siro20/P1P2_HBS_USBCdc_Modem/kicad/p1p2_pi_hat.png

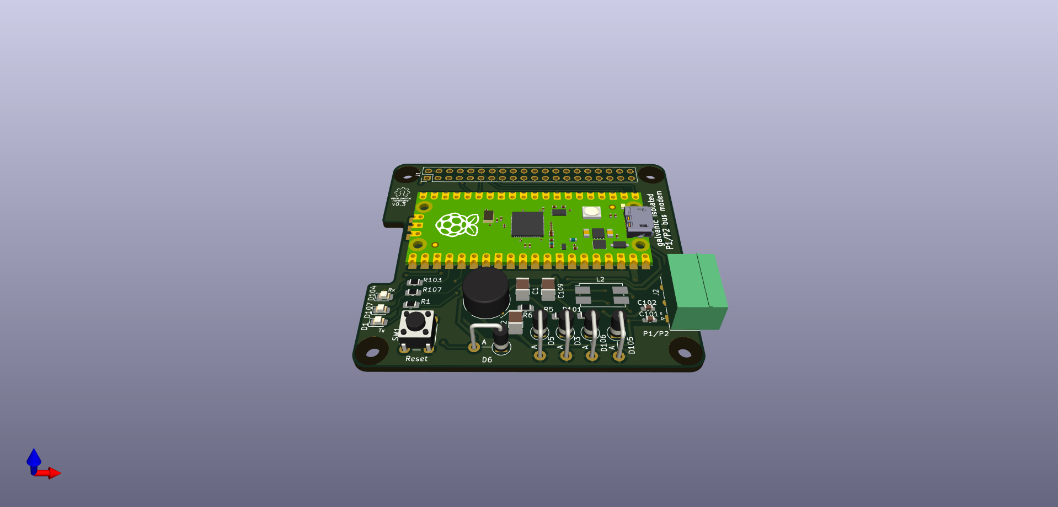
kicad/p1p2_pi_hat.png
