siro20/P1P2_HBS_USBCdc_Modem/pico/src/shiftreg.hpp

#pragma once
#include "inttypes.h"
#include <string.h>
#include <cassert>
#include <iostream>

template <class T, size_t N>
class ShiftReg
{
  public:

    // Implements a shift register on top of a fixed size circular buffer
    // The buffer has twice the requested size to prevent wrapping around.
    // This allows to return a pointer to a linear buffer with zero copy.
    // By pushing a new value into the shift register the oldest value is poped
    // If init is NULL the register will be zero'd, else the contents are initialized.
    ShiftReg(T buffer[N * 2], const T *init) :  data(buffer), off(0) {
        assert(init != nullptr);
        assert(buffer != nullptr);

        for (size_t i = 0; i < N; i++) {
            this->data[i] = init[i];
            this->data[i + N] = init[i];
        }
    }

    ShiftReg(T buffer[N * 2]) : data(buffer), off(0) {
        assert(buffer != nullptr);
        memset(buffer, 0, sizeof(T) * N * 2);
    }
    // Update returns false if no new data is available.
    // Update returns true if new data has been placed in out.
    bool Update(const T in, T *out)  {
        T *ptr;
        if (out)
            *out = this->data[this->off];
        assert(this->off < N);

        ptr = &this->data[this->off];
        // Pointer magic generates smaller code
        ptr[0] = in;
        ptr[N] = in;

        this->off++;
        if (this->off == N)
            this->off = 0;
        return true;
    }

    // Update returns false if no new data is available.
    // Update returns true if new data has been placed in out.
    bool Update(const T in)  {
        T *ptr;
        ptr = &this->data[this->off];
        // Pointer magic generates smaller code
        ptr[0] = in;
        ptr[N] = in;

        this->off++;
        if (this->off == N)
            this->off = 0;
        return true;
    }

    uint32_t Length(void) {
        return N;
    }

    // At returns the data at given position
    // 0 is the oldest entry and length-1 is the latest
    inline T At(const uint32_t i) {
        if (i >= N) {
            assert(i < N);
        }
        // Get offset into circular buffer
        // As it has twice the specified size it never overflows
        // and doesn't need to wrap around.
        return this->data[i + this->off];
    }

    // Data returns a pointer to the data.
    // The caller can assume that the returned buffer is N items big.
    // The first item is the oldest entry and length-1 is the latest.
    inline T* Data() {
        // Get offset into circular buffer
        // As it has twice the specified size it never overflows
        // and doesn't need to wrap around.
        return &this->data[this->off];
    }

    // Folds the shift register with another shift register.
    // If the length of both shift register is not equal, it only folds the
    // smaller register full set of data.
    //
    // The caller must make sure that the result doesn't overflow, i.e. by reducing
    // the signal amplitude before calling this function.
    template<typename A, typename B, size_t X, size_t Y>
    static int32_t Convolute(ShiftReg<A, X>& a, ShiftReg<B, Y>& b)
    {
        uint32_t min, i;
        int32_t result = 0;
        A *ptr_a = a.Data();
        B *ptr_b = b.Data();

        min = (a.Length() < b.Length()) ? a.Length() : b.Length();

        for (i = 0; i < min; i++) {
            // Pointer magic generates smaller code
            result += ptr_a[0] * ptr_b[0];
            ptr_a++;
            ptr_b++;
        }
        return result;
    }

  private:
    T *data;
    uint32_t off;
};
