siro20/P1P2_HBS_USBCdc_Modem/pico/src/host_uart.hpp

#include "fifo_irqsafe.hpp"
#include "line_receiver_irqsafe.hpp"

#include "message.hpp"

#define MAX_PACKET_SIZE 32

// High level abstraction of UART
class HostUART
{
	public:
		HostUART(void);
		~HostUART(void);

		static HostUART& getInstance(void)
		{
			__scratch_y("host_uart_instance") static HostUART instance;
			return instance;
		}

		HostUART(HostUART const&) = delete;
		void operator=(HostUART const&) = delete;

		enum UART_PARITY {
			PARITY_NONE = 0,
			PARITY_EVEN,
			PARITY_ODD,
		};

		void OnLineReceived(char *line);

		void UpdateAndSend(Message& m);
		void Send(Message& m);
		Message PopExtController(void);
		Message PopGeneric(void);

		void Check(void);
		bool HasDataExtController(void);
		bool HasDataGeneric(void);

		void CheckRXFIFO(void);
		void CheckTXFIFO(void);
	private:

		// error is true on buffer overrun. Should never happen.
		bool error;
		FifoIrqSafe<uint8_t, 128> tx_fifo;
		LineReceiverIrqSafe<char, 128> rx_fifo;
		FifoIrqSafe<Message, 8> rx_msgs_ext_ctrl;
		FifoIrqSafe<Message, 8> rx_msgs_generic;
};
