siro20/P1P2_HBS_USBCdc_Modem/pico/src/line_receiver_irqsafe.hpp

#pragma once
#include "hardware/sync.h"
#include "inttypes.h"
#include <string.h>
#include <cassert>
#include <iostream>

template <class T, size_t N>
class LineReceiverIrqSafe
{
  public:

    LineReceiverIrqSafe(const T *init) : data{}, off(N) {
        assert(init != nullptr);

        for (size_t i = 0; i < N; i++) {
            this->data[i] = init[i];
        }
    }

    LineReceiverIrqSafe() : data{}, off(0) {
    }

    // Push returns true if new data has been successfully
    // been stored. false if there was not enough space.
    bool Push(const T in)  {
        uint32_t save = save_and_disable_interrupts();

        if (this->off < N) {
            this->data[this->off] = in;
            this->off++;
            __dmb();
            restore_interrupts(save);

            return true;
        }

        restore_interrupts(save);
        return false;
    }

    uint32_t Length(void) {
        uint32_t ret;
        uint32_t save = save_and_disable_interrupts();
        ret = this->off;
        restore_interrupts(save);
        return ret;
    }

    bool Empty(void) {
        return this->Length() == 0;
    }

    bool Full(void) {
        return this->Length() == N;
    }

     void Clear(void) {
        uint32_t save = save_and_disable_interrupts();
        this->off = 0;
        restore_interrupts(save);
    }

    // At returns the data at given position
    // 0 is the oldest entry and length-1 is the latest
    inline T At(const uint32_t i) {
        T ret;
        uint32_t save = save_and_disable_interrupts();
        if (i >= N) {
            assert(i < N);
        }

        ret = this->data[i];
        restore_interrupts(save);
        return ret;
    }

    inline T *Data(void) {
        return this->data;
    }
  private:
    T data[N];
    uint32_t off;
};
