siro20/P1P2_HBS_USBCdc_Modem/pico/src/fir_filter.cpp

#include <stdexcept>
#include "fir_filter.hpp"
#include "math.h"
#include <iostream>
using namespace std;

// The compiler generates sub-optimal code when using 16bit data types....

static const int32_t coefficients[] = {
	-0.071383729317764918 * 0x7fff,
	0.055470186813273974 * 0x7fff,
	0.304697734025869083 * 0x7fff,
	0.436830215005959033 * 0x7fff,
	0.304697734025869138 * 0x7fff,
	0.055470186813273988 * 0x7fff,
	-0.071383729317764918 * 0x7fff,

	-0.071383729317764918 * 0x7fff,
	0.055470186813273974 * 0x7fff,
	0.304697734025869083 * 0x7fff,
	0.436830215005959033 * 0x7fff,
	0.304697734025869138 * 0x7fff,
	0.055470186813273988 * 0x7fff,
	-0.071383729317764918 * 0x7fff,
};

FIRFilter::FIRFilter(int32_t buffer_a[7 * 2], int32_t buffer_b[7 * 2]) :
reg(buffer_a), coeff(buffer_b, coefficients)
{
}

// Update returns false if no new data is available.
// Update returns true if new data has been placed in out.
bool FIRFilter::Update(const int32_t in, int32_t *out) {
	int32_t tmp;
	// Shift in new value
	this->reg.Update(in);

	// Apply the filter
	tmp = ShiftReg<int32_t, 7>::Convolute<int32_t,int32_t, 7, 7>(this->reg, this->coeff);
	*out = tmp >> 15;
	return true;
}
