siro20/P1P2_HBS_USBCdc_Modem/pico/tests/uart_test.cpp

#include <gtest/gtest.h>

#include "uart.hpp"
#include "level_detect.hpp"
#include "uart_bit_detect_fast.hpp"

#define OVERSAMPLING 16

// Captured waveform from hardware
static int16_t testdata[] = {
0,
3000,
3000,
3000,
3000,
3000,
3000,
1500,
0,
0,
0,
-26,
-30,
-44,
-51,
11,
-149,
-1860,
-3046,
-3029,
-3003,
-2995,
-2997,
-3029,
-2954,
-1440,
-46,
20,
-21,
-5,
-5,
-65,
296,
2112,
3160,
3126,
3102,
3073,
3074,
3130,
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

};

static void genTestData(uint8_t b, enum UART::UART_PARITY p, int16_t data[OVERSAMPLING * 13]) {
	size_t off, toggle, parity;
	for (size_t i = 0; i < OVERSAMPLING * 13; i++) {
		data[i] = 0;
	}

	off = OVERSAMPLING;
	toggle = 1;

	/* Start */
	for (size_t i = 0; i < OVERSAMPLING / 2; i++) {
		data[i + off] = 3300 * toggle;
	}
	toggle *= -1;

	off += OVERSAMPLING;
	parity = 0;

	/* Data LSB first */
	for (ssize_t bit = 0; bit < 8; bit++, off+=OVERSAMPLING) {
		if (!(b & (1 << bit))) {
			for (size_t i = 0; i < OVERSAMPLING / 2; i++) {
				data[i + off] = 3300 * toggle;
			}
			toggle *= -1;
		} else {
			parity++;
		}
	}
	/* Parity */
	if ((p == UART::PARITY_EVEN) && !(parity & 1)) {
		// Parity is even, send 0
		for (size_t i = 0; i < OVERSAMPLING / 2; i++) {
			data[i + off] = 3300 * toggle;
		}
		toggle *= -1;
	}
	if ((p == UART::PARITY_ODD) && ((parity & 1) > 0)) {
		// Parity is odd, send 0
		for (size_t i = 0; i < OVERSAMPLING / 2; i++) {
			data[i + off] = 3300 * toggle;
		}
		toggle *= -1;
	}

	//std::cout << "testdata:" << std::endl;
	//for (size_t i = 0; i < OVERSAMPLING * 13; i++) {
	//	std::cout << data[i] << " ";
	//}
	//std::cout << std::endl;
}

TEST(UART, TestDecodeParityNone)
{
	int32_t buf_uart_bit1[UART_OVERSAMPLING_RATE * 2];
	int32_t buf_uart_bit2[UART_OVERSAMPLING_RATE * 2];
	UARTBit<int32_t, UART_OVERSAMPLING_RATE> b(buf_uart_bit1, buf_uart_bit2, BUS_HIGH_MV, BUS_LOW_MV, 0xE0);
	int16_t buf[UART_BUFFER_LEN * 2];
	UART u(buf, UART::PARITY_NONE);
	uint8_t out;
	bool err;
	bool done;
	int16_t p[OVERSAMPLING * 13];
	int uart_active;
	int32_t signal;

	for (uint16_t testbyte = 0; testbyte <= 0xff; testbyte++) {
		genTestData(testbyte, UART::PARITY_NONE, p);

		uart_active = 0;
		for (size_t i = 0; i < OVERSAMPLING * 13; i++) {	
			out = 0;
			err = false;
			b.Update(p[i], &signal);
			done = u.Update(signal, &out, &err);
			if (done)
				break;
			if (u.Receiving())
				uart_active++;
		}

		EXPECT_GT(uart_active, 9 * OVERSAMPLING);
		EXPECT_EQ(done, true);
		EXPECT_EQ(err, false);
		EXPECT_EQ(testbyte, out);
	}
}

TEST(UART, TestFramingError)
{
	int32_t buf_uart_bit1[UART_OVERSAMPLING_RATE * 2];
	int32_t buf_uart_bit2[UART_OVERSAMPLING_RATE * 2];
	UARTBit<int32_t, UART_OVERSAMPLING_RATE> b(buf_uart_bit1, buf_uart_bit2, BUS_HIGH_MV, BUS_LOW_MV, 0xE0);
	int16_t buf[UART_BUFFER_LEN * 2];
	UART u(buf, UART::PARITY_NONE);
	uint8_t out;
	bool err;
	bool done;
	int16_t p[OVERSAMPLING * 13];
	int32_t signal;

	for (uint16_t testbyte = 0; testbyte <= 0xff; testbyte++) {
		genTestData(testbyte, UART::PARITY_NONE, p);

		// Break STOP bit
		for (size_t i = (OVERSAMPLING * 10); i < (OVERSAMPLING * 10 + OVERSAMPLING/2); i++)
			p[i] = 3300;

		for (size_t i = 0; i < OVERSAMPLING * 13; i++) {	
			out = 0;
			err = false;
			b.Update(p[i], &signal);
			done = u.Update(signal, &out, &err);
			if (done)
				break;
		}

		EXPECT_EQ(done, true);
		EXPECT_EQ(err, true);
	}
}

TEST(UART, TestPolarityError)
{
	int32_t buf_uart_bit1[UART_OVERSAMPLING_RATE * 2];
	int32_t buf_uart_bit2[UART_OVERSAMPLING_RATE * 2];
	UARTBit<int32_t, UART_OVERSAMPLING_RATE> b(buf_uart_bit1, buf_uart_bit2, BUS_HIGH_MV, BUS_LOW_MV, 0xE0);
	int16_t buf[UART_BUFFER_LEN * 2];
	UART u(buf, UART::PARITY_EVEN);
	uint8_t out;
	bool err;
	bool done;
	int16_t p[OVERSAMPLING * 13];
	int32_t signal;

	for (uint16_t testbyte = 0; testbyte <= 0xff; testbyte++) {
		genTestData(testbyte, UART::PARITY_EVEN, p);

		// Invert START bit polarity
		for (size_t i = (OVERSAMPLING * 1); i < (OVERSAMPLING * 1 + OVERSAMPLING/2); i++)
			p[i] = -p[i];

		for (size_t i = 0; i < OVERSAMPLING * 13; i++) {	
			out = 0;
			err = false;
			b.Update(p[i], &signal);
			done = u.Update(signal, &out, &err);
			if (done)
				break;
		}

		EXPECT_EQ(done, true);
		EXPECT_EQ(err, true);
	}
}

TEST(UART, TestDecodeParityEven)
{
	int32_t buf_uart_bit1[UART_OVERSAMPLING_RATE * 2];
	int32_t buf_uart_bit2[UART_OVERSAMPLING_RATE * 2];
	UARTBit<int32_t, UART_OVERSAMPLING_RATE> b(buf_uart_bit1, buf_uart_bit2, BUS_HIGH_MV, BUS_LOW_MV, 0xE0);
	int16_t buf[UART_BUFFER_LEN * 2];
	UART u(buf, UART::PARITY_EVEN);
	uint8_t out;
	bool err;
	bool done;
	int16_t p[OVERSAMPLING * 13];
	int uart_active;
	int32_t signal;

	// Test all bytes with correct parity
	for (uint16_t testbyte = 0; testbyte <= 0xff; testbyte++) {
		genTestData(testbyte, UART::PARITY_EVEN, p);

		uart_active = 0;
		for (size_t i = 0; i < OVERSAMPLING * 13; i++) {	
			out = 0;
			err = false;
			b.Update(p[i], &signal);
			done = u.Update(signal, &out, &err);
			if (done)
				break;
			if (u.Receiving())
				uart_active++;
		}

		EXPECT_GT(uart_active, 10 * OVERSAMPLING);
		EXPECT_EQ(done, true);
		EXPECT_EQ(err, false);
		EXPECT_EQ(testbyte, out);
	}
	// Test all bytes with incorrect parity
	for (uint16_t testbyte = 0; testbyte <= 0xff; testbyte++) {
		genTestData(testbyte, UART::PARITY_ODD, p);

		for (size_t i = 0; i < OVERSAMPLING * 13; i++) {	
			out = 0;
			err = false;
			done = u.Update(p[i], &out, &err);
			if (done)
				break;
		}

		EXPECT_EQ(done, true);
		EXPECT_EQ(err, true);
	}
}

TEST(UART, TestDecodeParityOdd)
{
	int32_t buf_uart_bit1[UART_OVERSAMPLING_RATE * 2];
	int32_t buf_uart_bit2[UART_OVERSAMPLING_RATE * 2];
	UARTBit<int32_t, UART_OVERSAMPLING_RATE> b(buf_uart_bit1, buf_uart_bit2, BUS_HIGH_MV, BUS_LOW_MV, 0xE0);
	int16_t buf[UART_BUFFER_LEN * 2];
	UART u(buf, UART::PARITY_ODD);
	uint8_t out;
	bool err;
	bool done;
	int16_t p[OVERSAMPLING * 13];
	int uart_active;
	int32_t signal;

	// Test all bytes with correct parity
	for (uint16_t testbyte = 0; testbyte <= 0xff; testbyte++) {
		genTestData(testbyte, UART::PARITY_ODD, p);

		uart_active = 0;
		for (size_t i = 0; i < OVERSAMPLING * 13; i++) {
	
			out = 0;
			err = false;
			b.Update(p[i], &signal);
			done = u.Update(signal, &out, &err);
			if (done)
				break;
			if (u.Receiving())
				uart_active++;
		}

		EXPECT_GT(uart_active, 10 * OVERSAMPLING);
		EXPECT_EQ(done, true);
		EXPECT_EQ(err, false);
		EXPECT_EQ(testbyte, out);
	}
	// Test all bytes with incorrect parity
	for (uint16_t testbyte = 0; testbyte <= 0xff; testbyte++) {
		genTestData(testbyte, UART::PARITY_EVEN, p);

		for (size_t i = 0; i < OVERSAMPLING * 13; i++) {
	
			out = 0;
			err = false;
			done = u.Update(p[i], &out, &err);
			if (done)
				break;
		}

		EXPECT_EQ(done, true);
		EXPECT_EQ(err, true);
	}
}

TEST(UART, TestPulseNoise)
{
	int32_t buf_uart_bit1[UART_OVERSAMPLING_RATE * 2];
	int32_t buf_uart_bit2[UART_OVERSAMPLING_RATE * 2];
	UARTBit<int32_t, UART_OVERSAMPLING_RATE> b(buf_uart_bit1, buf_uart_bit2, BUS_HIGH_MV, BUS_LOW_MV, 0xE0);
	int16_t buf[UART_BUFFER_LEN * 2];
	UART u(buf, UART::PARITY_ODD);

	uint8_t out;
	bool err;
	bool done;
	int16_t p[OVERSAMPLING * 13];
	int32_t signal;

	for (int16_t noise = 0; noise < OVERSAMPLING * 13; noise++) {
		genTestData(0xcc, UART::PARITY_ODD, p);

		// Inject spike
		p[noise] += 2500;
		p[noise+1] -= 2500;
		for (size_t i = 0; i < OVERSAMPLING * 13; i++) {
			out = 0;
			err = false;
			b.Update(p[i], &signal);
			done = u.Update(signal, &out, &err);
			if (done)
				break;
		}
		EXPECT_EQ(done, true);
		EXPECT_EQ(err, false);
		EXPECT_EQ(0xcc, out);
		// Print detailed report
		if (err || out != 0xcc) {
			for (ssize_t i = -32; i < 32; i++) {
				if (noise + i > 0 && noise + i < OVERSAMPLING * 13) {
					std::cerr << "[          ] p[" << noise + i << "] = " << p[noise + i] << std::endl;
				}
			}
			std::cerr << std::endl;
			p[noise] -= 2500;
			p[noise+1] += 2500;
			std::cerr << "[          ] was: " << std::endl;
			for (ssize_t i = -32; i < 32; i++) {
				if (noise + i > 0 && noise + i < OVERSAMPLING * 13)
					std::cerr << "[          ] p[" << noise + i << "] = " << p[noise + i] << std::endl;
			}
			std::cerr << "[          ] noise = " << noise << std::endl;
		}
	}
}

TEST(UART, TestCapturedTestData)
{
	int32_t buf_uart_bit1[UART_OVERSAMPLING_RATE * 2];
	int32_t buf_uart_bit2[UART_OVERSAMPLING_RATE * 2];
	UARTBit<int32_t, UART_OVERSAMPLING_RATE> b(buf_uart_bit1, buf_uart_bit2, BUS_HIGH_MV, BUS_LOW_MV, 0xE0);
	int16_t buf[UART_BUFFER_LEN * 2];
	UART u(buf, UART::PARITY_EVEN);
	Level<int32_t> l;
	int32_t signal;
	uint8_t out;
	bool err;
	int count = 0;

	for (size_t i = 0; i < sizeof(testdata)/sizeof(testdata[0]); i++) {
		out = 0xff;
		err = false;
		l.Update(testdata[i], &signal);
		b.Update(signal, &signal);
		if (u.Update(signal, &out, &err)) {

			EXPECT_EQ(count, out);
			if (err)
				std::cerr << "[          ] i = " << i << std::endl;
			EXPECT_EQ(err, false);

			count++;

		}
	}

	EXPECT_EQ(count, 3);

}
