siro20/P1P2_HBS_USBCdc_Modem/pico/tests/uart_bit_detect_test.cpp

#include <gtest/gtest.h>
#include <math.h>

#include "uart_bit_detect_fast.hpp"
#include "level_detect.hpp"

#define LVL_HIGH 1400
#define LVL_LOW 600

TEST(UartBitDetect, TestRealWorldHigh)
{
	int16_t buf_a[16 * 2];
	int16_t buf_b[16 * 2];
	UARTBit<int16_t, 16> b(buf_a, buf_b, LVL_HIGH, LVL_LOW, 0xe0);
	Level<int16_t> l;

	int16_t data[16];
	int16_t out[16];

	memset(data, 0, sizeof(*data) * 16);
	for (size_t i = 1; i < 9; i++) {
		data[i] = LVL_HIGH;
	}
	for (size_t i = 9; i < 17; i++) {
		data[i] = LVL_LOW - 1;
	}
	
	for (size_t i = 0; i < 16; i++) {
		b.Update(data[i], &out[i]);
	}

	EXPECT_EQ(out[15], 6206);

	for (size_t i = 9; i < 17; i++) {
		data[i] = -LVL_LOW + 1;
	}
	
	for (size_t i = 0; i < 16; i++) {
		b.Update(data[i], &out[i]);
	}

	EXPECT_EQ(out[15], 6206);
}

TEST(UartBitDetect, TestRealWorldLow)
{
	int16_t buf_a[16 * 2];
	int16_t buf_b[16 * 2];
	UARTBit<int16_t, 16> b(buf_a, buf_b, LVL_HIGH, LVL_LOW, 0xe0);
	Level<int16_t> l;

	int16_t data[16];
	int16_t out[16];

	memset(data, 0, sizeof(*data) * 16);
	for (size_t i = 1; i < 9; i++) {
		data[i] = -LVL_HIGH;
	}
	for (size_t i = 9; i < 17; i++) {
		data[i] = -LVL_LOW + 1;
	}
	
	for (size_t i = 0; i < 16; i++) {
		b.Update(data[i], &out[i]);
	}

	EXPECT_EQ(out[15], -6206);

	for (size_t i = 9; i < 17; i++) {
		data[i] = LVL_LOW - 1;
	}
	
	for (size_t i = 0; i < 16; i++) {
		b.Update(data[i], &out[i]);
	}

	EXPECT_EQ(out[15], -6206);
}

TEST(UartBitDetect, High)
{
	int16_t buf_a[16 * 2];
	int16_t buf_b[16 * 2];
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
	}
	for (size_t i = 0; i < 16; i++) {
		b.Update(data[i], &out[i]);
	}
	EXPECT_EQ(out[14], 0);

	memset(data, 0, sizeof(*data) * 16);
	for (size_t i = 0; i < 16; i++) {
		data[i] = -LVL_HIGH;
	}
	for (size_t i = 0; i < 16; i++) {
		b.Update(data[i], &out[i]);
	}
	EXPECT_EQ(out[14], 0);
}
